nicolaeser/busylight-esp/streamdeck-plugin/busylight/org.igox.busylight.sdPlugin/imgs/actions/buttons/colored/colored.png

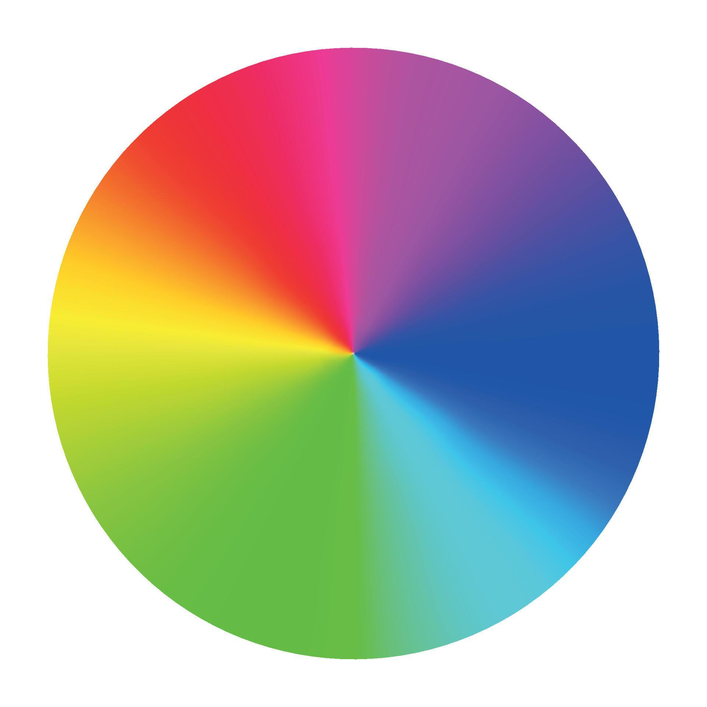
streamdeck-plugin/busylight/org.igox.busylight.sdPlugin/imgs/actions/buttons/colored/colored.png
