nicolaeser/busylight-esp/streamdeck-plugin/busylight/org.igox.busylight.sdPlugin/imgs/actions/buttons/on/on.png

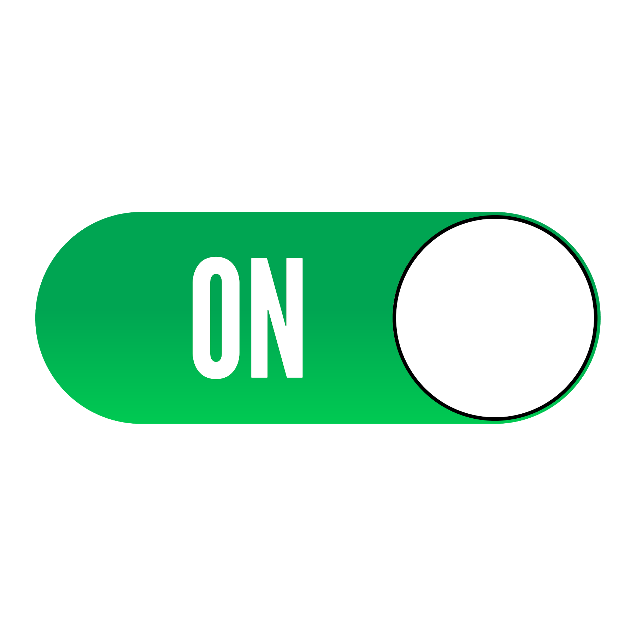
streamdeck-plugin/busylight/org.igox.busylight.sdPlugin/imgs/actions/buttons/on/on.png
